aayushpataskar/Sensorless-BLDC-Motor-Controller-using-AVR/ckts/esc using arduino uno.kicad_sch

## KiCad design ckts/esc using arduino uno.kicad_sch (2026-05-27)

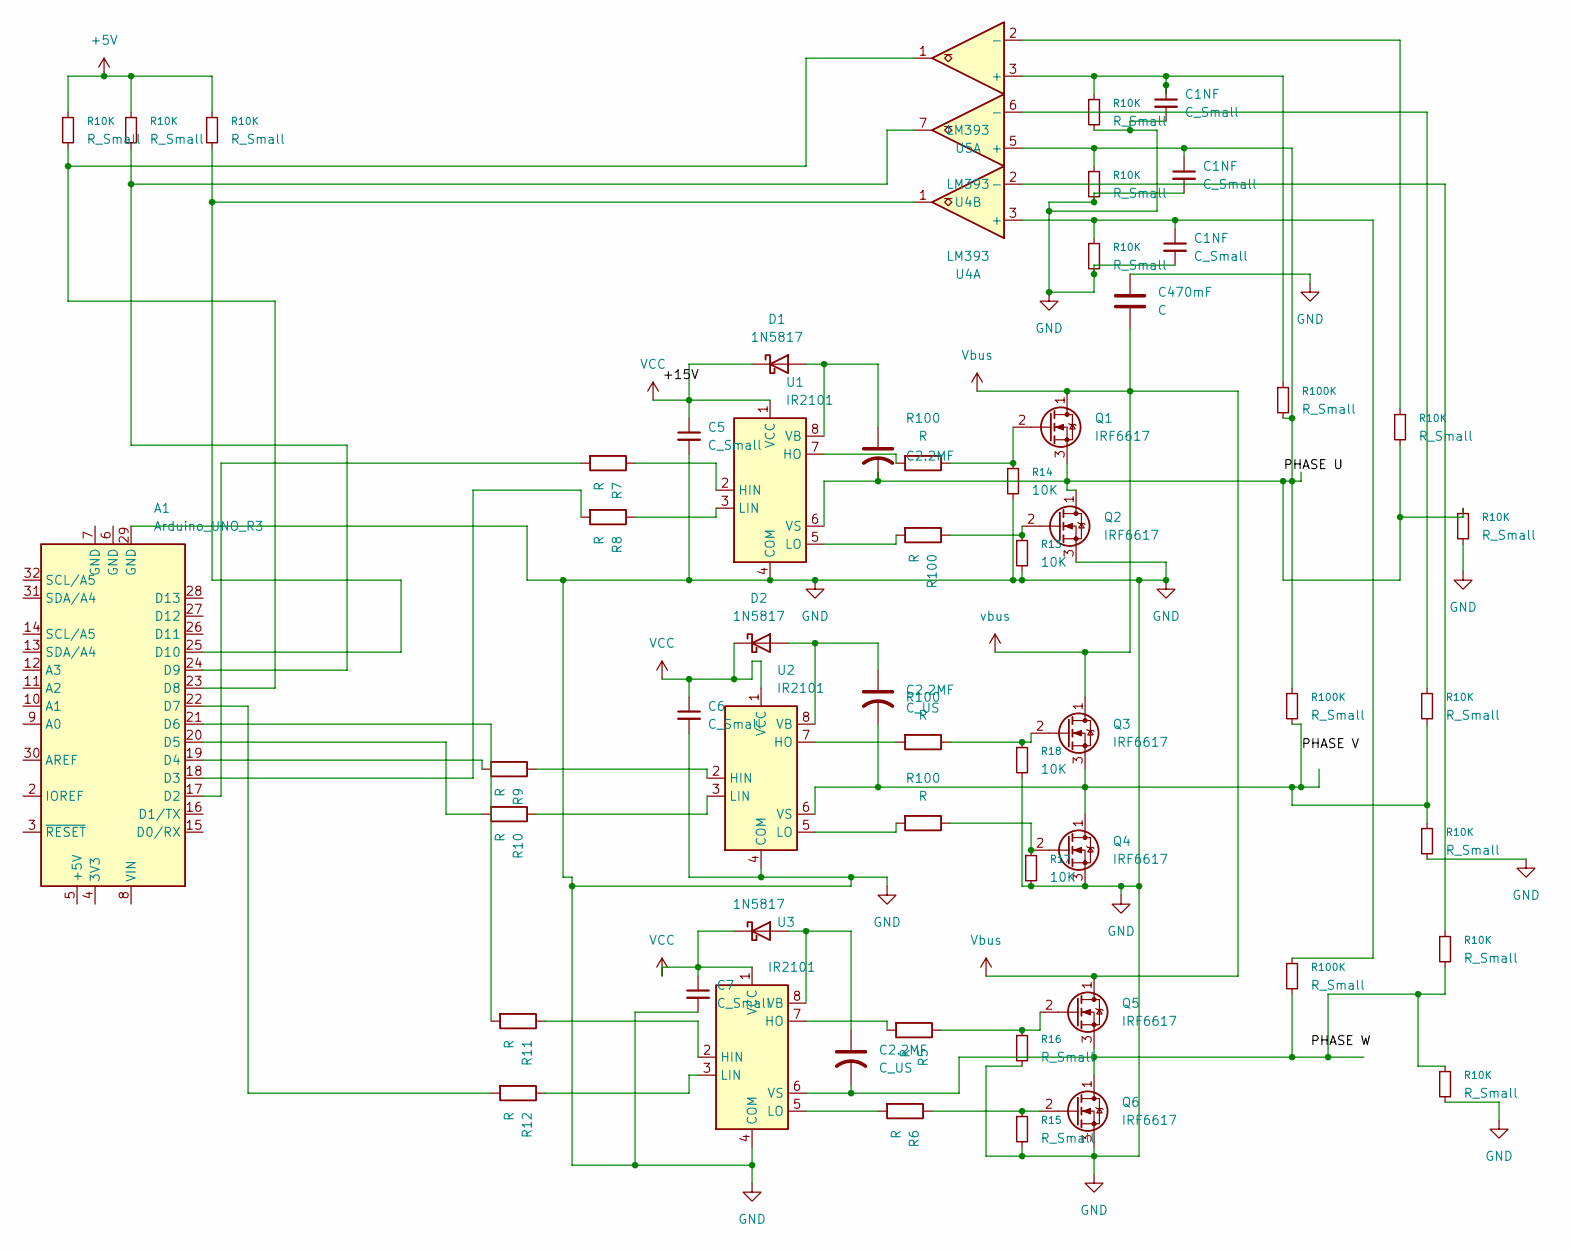
[picture p5: schematic esc using arduino uno.kicad_sch]

Parts:
A1: Arduino_UNO_R3
C1NF, C5, C6, C7: C_Small
C2.2MF: C_US
C470mF: C
D1, D2, D3: 1N5817; D_DO-41_SOD81_P10.16mm_Horizontal
Q1, Q2, Q3, Q4, Q5, Q6: IRF6617; DirectFET_ST
R5, R6, R7, R8, R9, R10, R11, R12, R100: R
R10K, R15, R16, R100K: R_Small
R13, R14, R17, R18: 10K
U1, U2, U3: IR2101
U4, U5: LM393

Connections:
+5V: R10K.1
GND: A1.29 (GND), C1NF.2, C5.2, C6.2, C7.2, C470mF.1, Q2.3 (S), Q4.3 (S), Q6.3 (S), R10K.2, R13.2, R14.2, R15.2, R16.2, R17.2, R18.2, U1.4 (COM), U2.4 (COM), U3.4 (COM)
unnamed: A1.17 (D2), R7.2
unnamed: A1.18 (D3), R8.2
unnamed: A1.19 (D4), R9.2
unnamed: A1.20 (D5), R10.2
unnamed: A1.21 (D6), R11.2
unnamed: A1.22 (D7), R12.2
unnamed: A1.23 (D8), R10K.2, U5.1
unnamed: A1.24 (D9), R10K.2, U4.7
unnamed: A1.25 (D10), R10K.2, U4.1
unnamed: C1NF.1, C2.2MF.2, Q1.3 (S), Q2.1 (D), R10K.1, R10K.2, R100K.1, R100K.2, U1.6 (VS), U4.3 (+), U4.5 (+), U5.3 (+)
unnamed: C2.2MF.1, D1.2 (A), D2.2 (A), D3.2 (A), U1.8 (VB), U2.8 (VB), U3.8 (VB)
unnamed: C2.2MF.2, Q5.3 (S), Q6.1 (D), R10K.1, R10K.2, R100K.2, U3.6 (VS)
unnamed: Q1.2 (G), R14.1, R100.1
unnamed: Q2.2 (G), R13.1, R100.1
unnamed: Q3.2 (G), R18.1, R100.1
unnamed: Q4.2 (G), R17.1, R100.1
unnamed: Q5.2 (G), R5.1, R16.1
unnamed: Q6.2 (G), R6.1, R15.1
unnamed: R5.2, U3.7 (HO)
unnamed: R6.2, U3.5 (LO)
unnamed: R7.1, U1.2 (HIN)
unnamed: R8.1, U1.3 (LIN)
unnamed: R9.1, U2.2 (HIN)
unnamed: R10.1, U2.3 (LIN)
unnamed: R10K.1, U4.2 (-), U4.6 (-), U5.2 (-)
unnamed: R11.1, U3.2 (HIN)
unnamed: R12.1, U3.3 (LIN)
unnamed: R100.2, U1.5 (LO), U1.7 (HO), U2.5 (LO), U2.7 (HO)
PHASE V: C2.2MF.2, Q3.3 (S), Q4.1 (D), R10K.1, R10K.2, R100K.2, U2.6 (VS)
VCC: C5.1, C6.1, C7.1, D1.1 (K), D2.1 (K), D3.1 (K), U1.1 (VCC), U2.1 (VCC), U3.1 (VCC)
Vbus: C470mF.2, Q1.1 (D), Q3.1 (D), Q5.1 (D)
